HorstBaerbel/GBA-mem/112.png

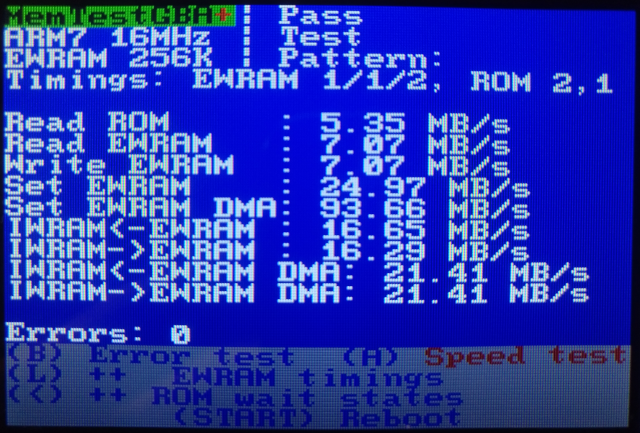
112.png
