HorstBaerbel/GBA-mem/336.png

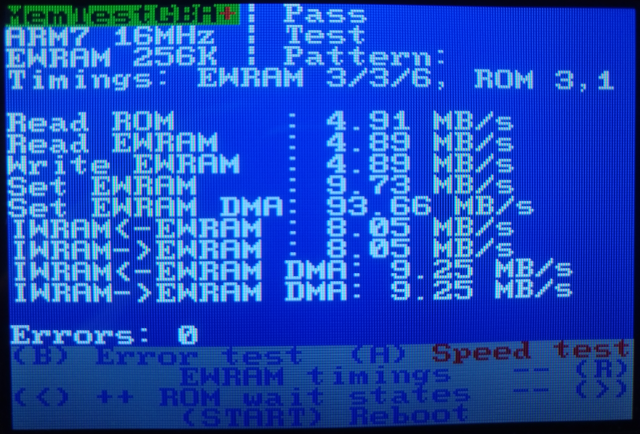
336.png
