HorstBaerbel/GBA-mem/KiCad/GBAmem.sch

## KiCad design KiCad/GBAmem.sch (2021-08-22, an earlier design)

Schematic: GBAmem.sch

Parts:
IC1: IS62WV12816EBLL-45TLI; SOP80P1176X120-44N; Mouser Part Number 870-6212816EBLL45TLI
U1: HY62LF16206A-LT12C; HY62LF16206A-LT12C_TSOP-I-48_12x18mm_Flip

Notes on the sheet:
D8-15 swapped for better placement
CS# -> GND /CS1 -> GND CS2 -> 3V3
